AmadeusW/icecold/program/src/modules/debugger.cpp

#include "Arduino.h"
#include "debugger.h"
#include "../module.h"
#include "../pins.h"

void Debugger::Setup() {
    pinMode(PinDebugLed, OUTPUT);
    digitalWrite(PinDebugLed, HIGH);

    Serial.println("Setup complete: Debug LED");
}

void Debugger::Output(int tick) {
    // Length in bits of supported codes
    int codeLength = 8;

    // Index of turn in the sequence of length codeLength
    int i = turn % codeLength;
    
    // Whether LED should be lit during the ith element of the sequence
    int lit = (code >> i) & 1;
    
    digitalWrite(PinDebugLed, lit);
}

void Debugger::SetCode(int code)
{
    this->code = code;
}
